evafc003/Mecatronica-Proyectos/Diagramas_y_Bocetos/Boceto_cascarrabias/RackandPinionGears(original)/images/RP_Cont_UpDown_Sz2.png

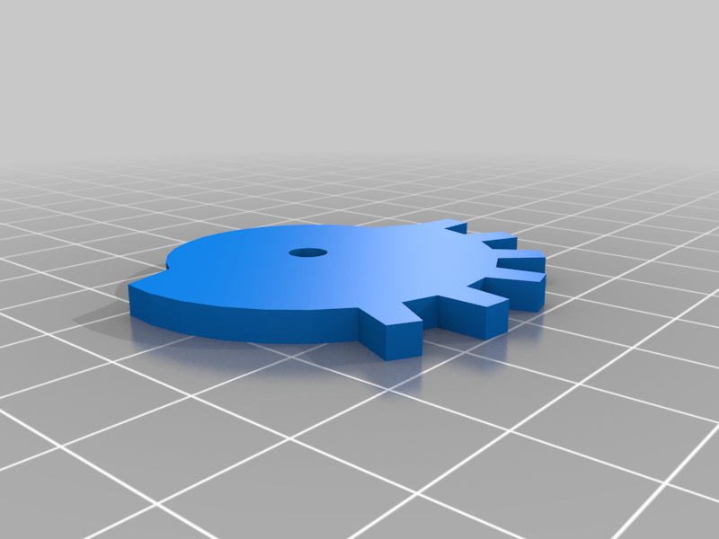
Diagramas_y_Bocetos/Boceto_cascarrabias/RackandPinionGears(original)/images/RP_Cont_UpDown_Sz2.png
