evafc003/Mecatronica-Proyectos/Diagramas_y_Bocetos/Diagrama_conexiones.png

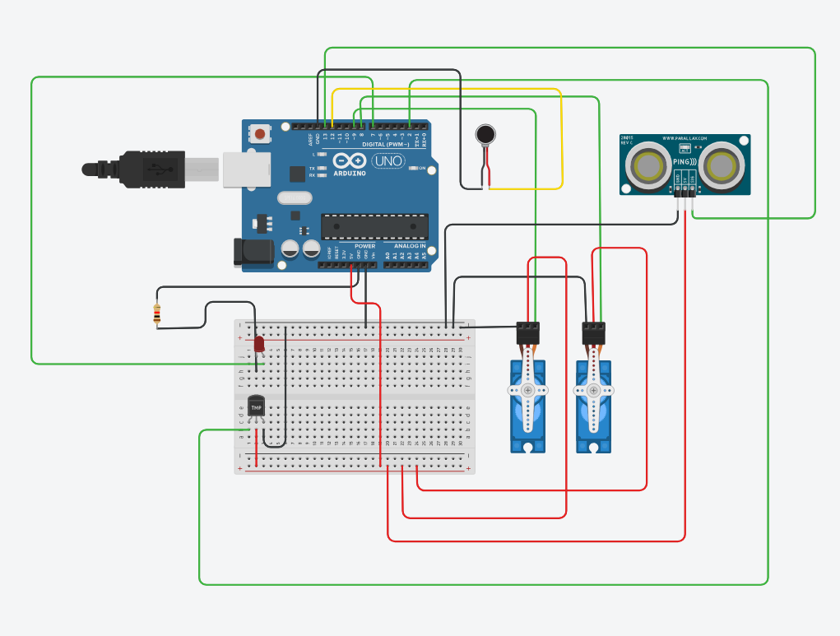
Diagramas_y_Bocetos/Diagrama_conexiones.png
