evafc003/Mecatronica-Proyectos/Multimedia/Fotos/caja_modificada.jpeg

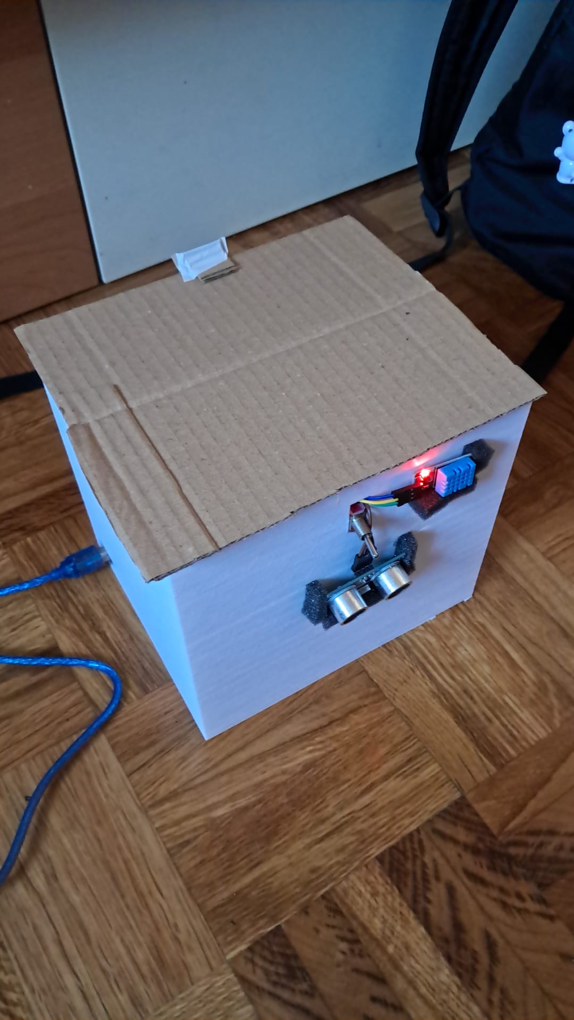
Multimedia/Fotos/caja_modificada.jpeg
