evafc003/Mecatronica-Proyectos/Multimedia/Fotos/cascarrabias_impreso.jpeg

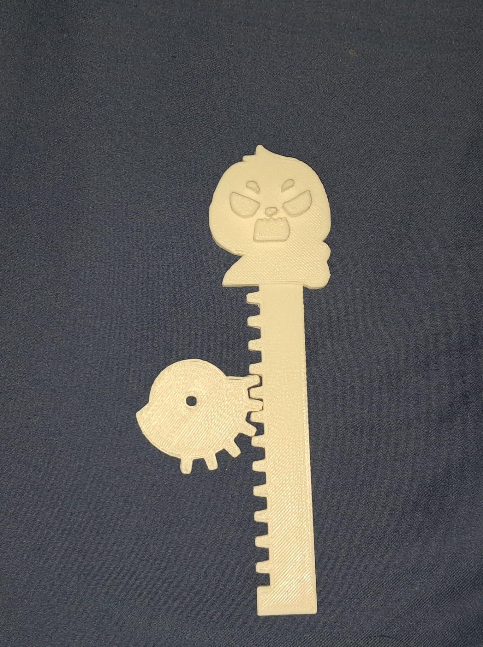
Multimedia/Fotos/cascarrabias_impreso.jpeg
