evafc003/Mecatronica-Proyectos/Multimedia/Fotos/montje_2_2.jpeg

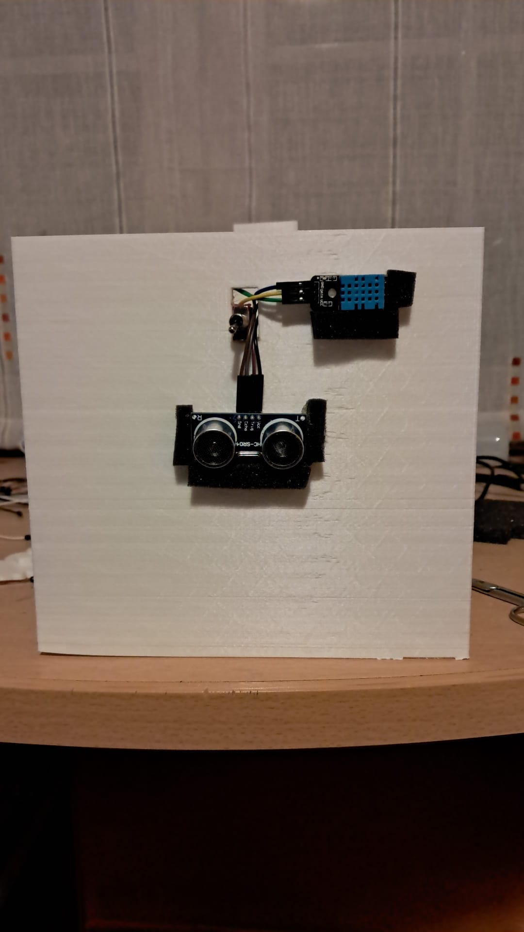
Multimedia/Fotos/montje_2_2.jpeg
