evafc003/Mecatronica-Proyectos/Multimedia/Fotos/Servo.png

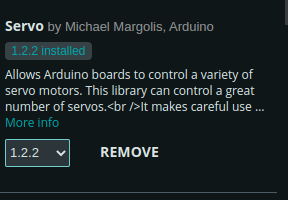
Multimedia/Fotos/Servo.png
