evafc003/Mecatronica-Proyectos/Multimedia/Fotos/tuto1.png

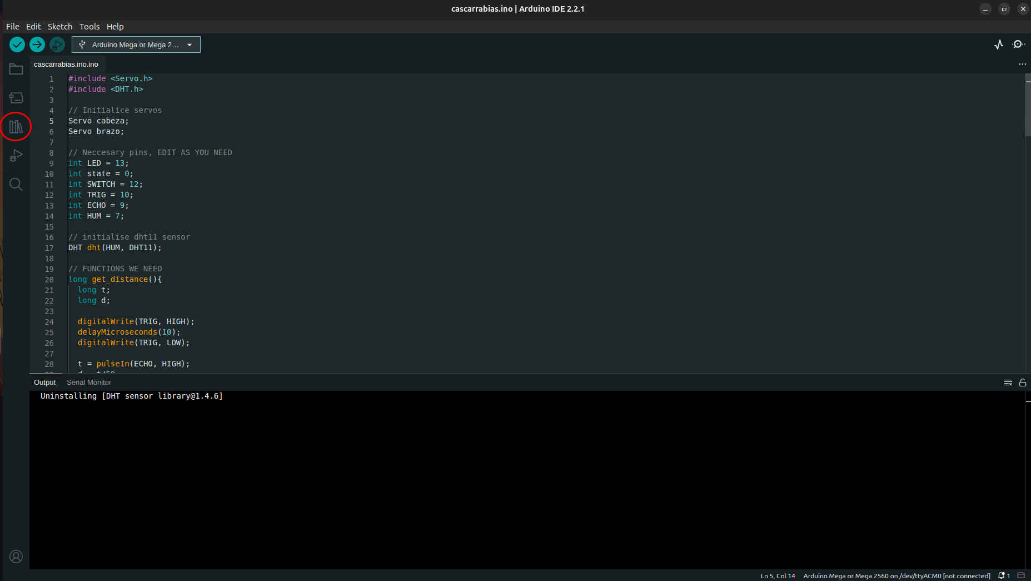
Multimedia/Fotos/tuto1.png
