evafc003/Mecatronica-Proyectos/Multimedia/Fotos/tuto2.png

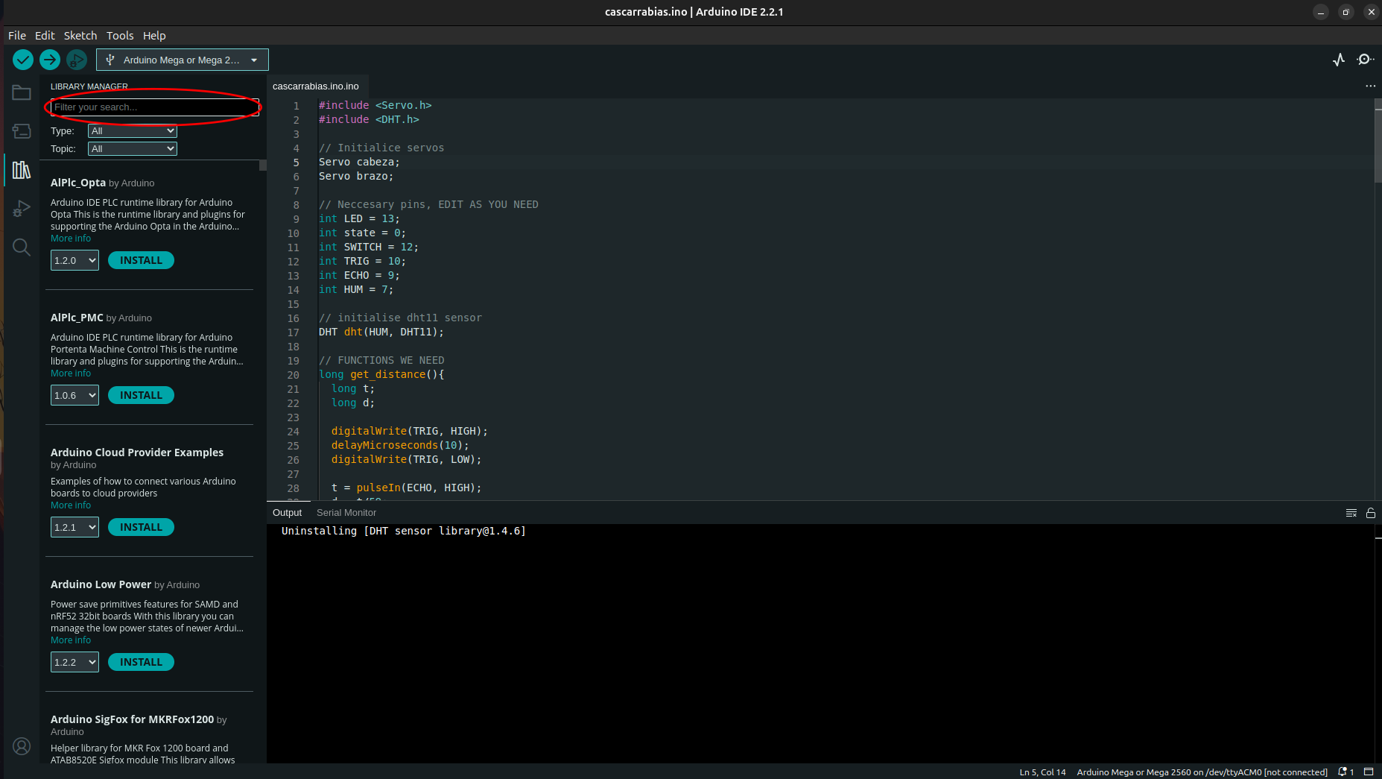
Multimedia/Fotos/tuto2.png
