evafc003/Mecatronica-Proyectos/Multimedia/Fotos/tuto5.png

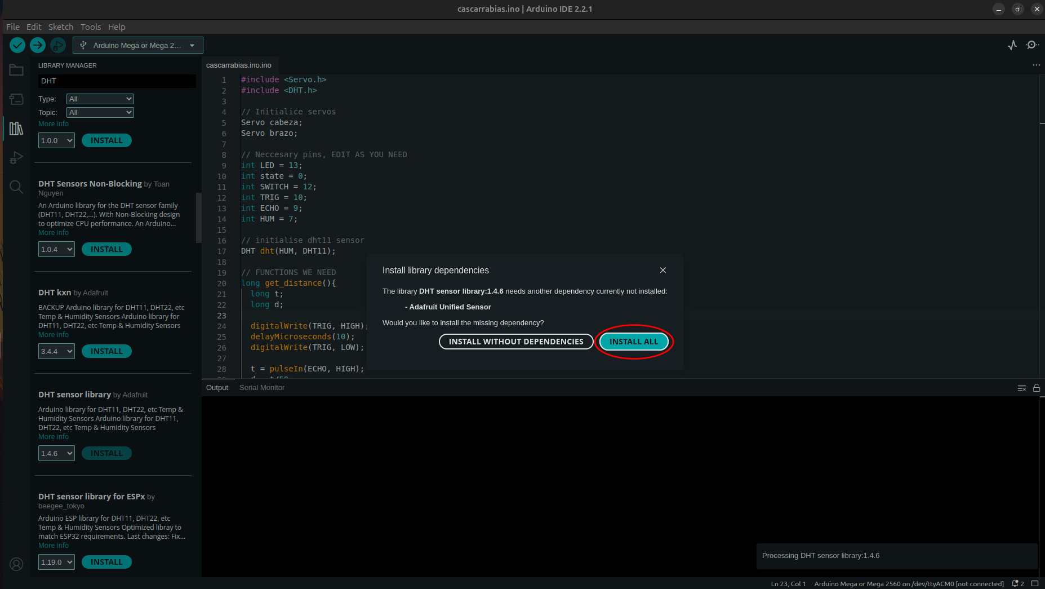
Multimedia/Fotos/tuto5.png
