evafc003/Mecatronica-Proyectos/Multimedia/Vídeos/mecanismo_brazo.gif

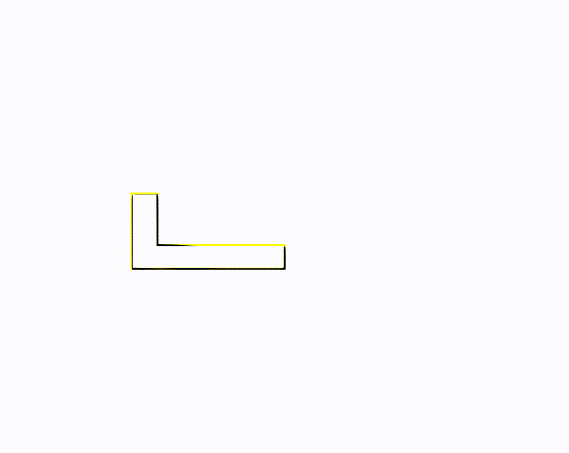
Multimedia/Vídeos/mecanismo_brazo.gif
