evafc003/Mecatronica-Proyectos/Planos/Planos_caja.jpeg

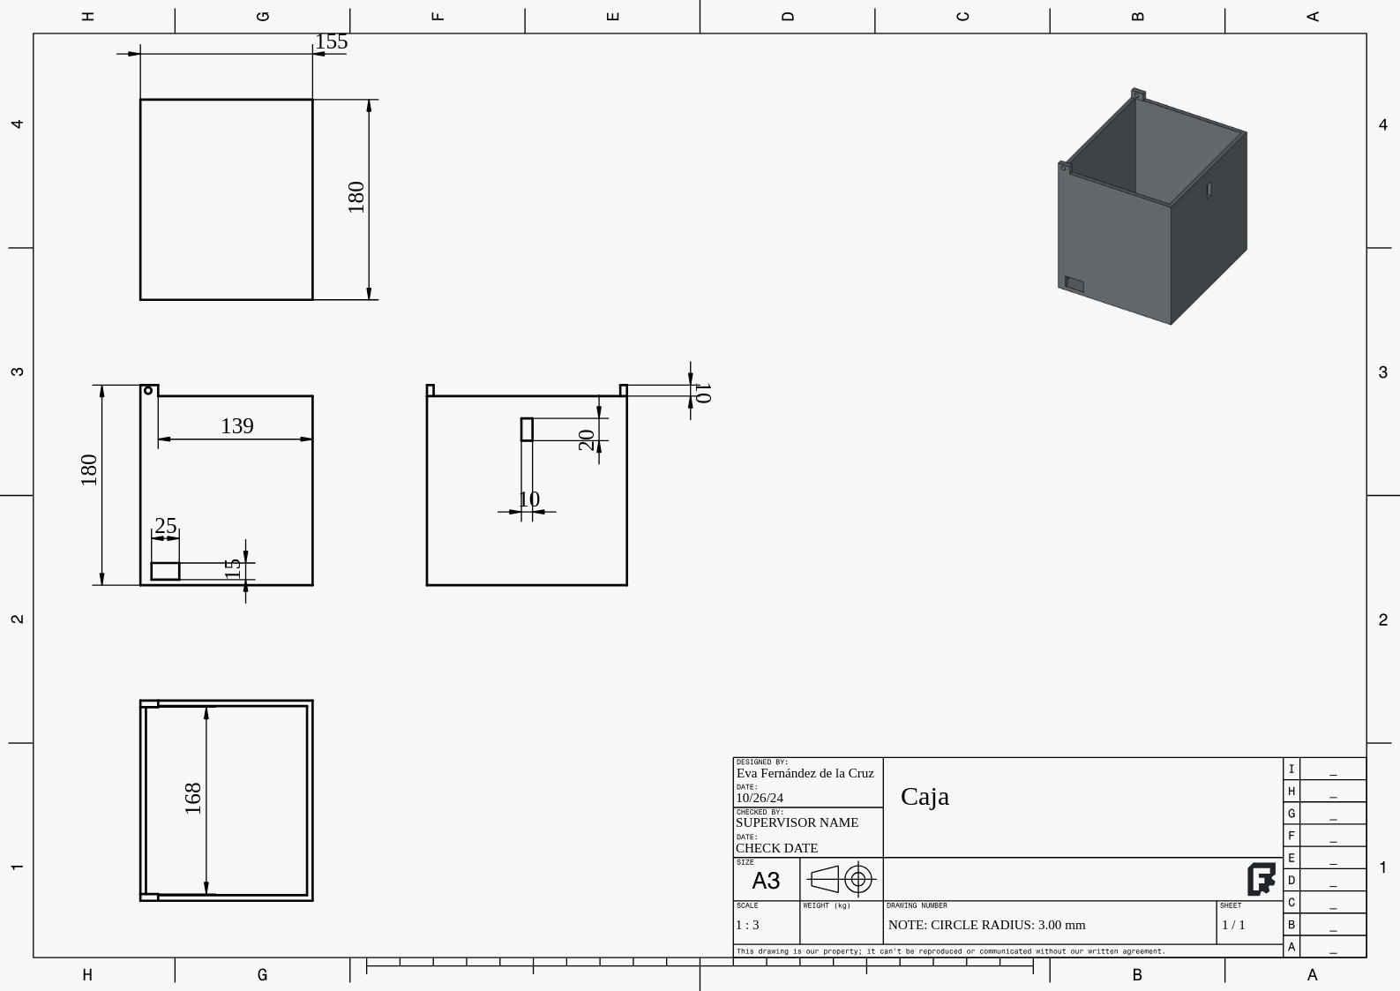
Planos/Planos_caja.jpeg
