evafc003/Mecatronica-Proyectos/Planos/Planos_tapa.jpeg

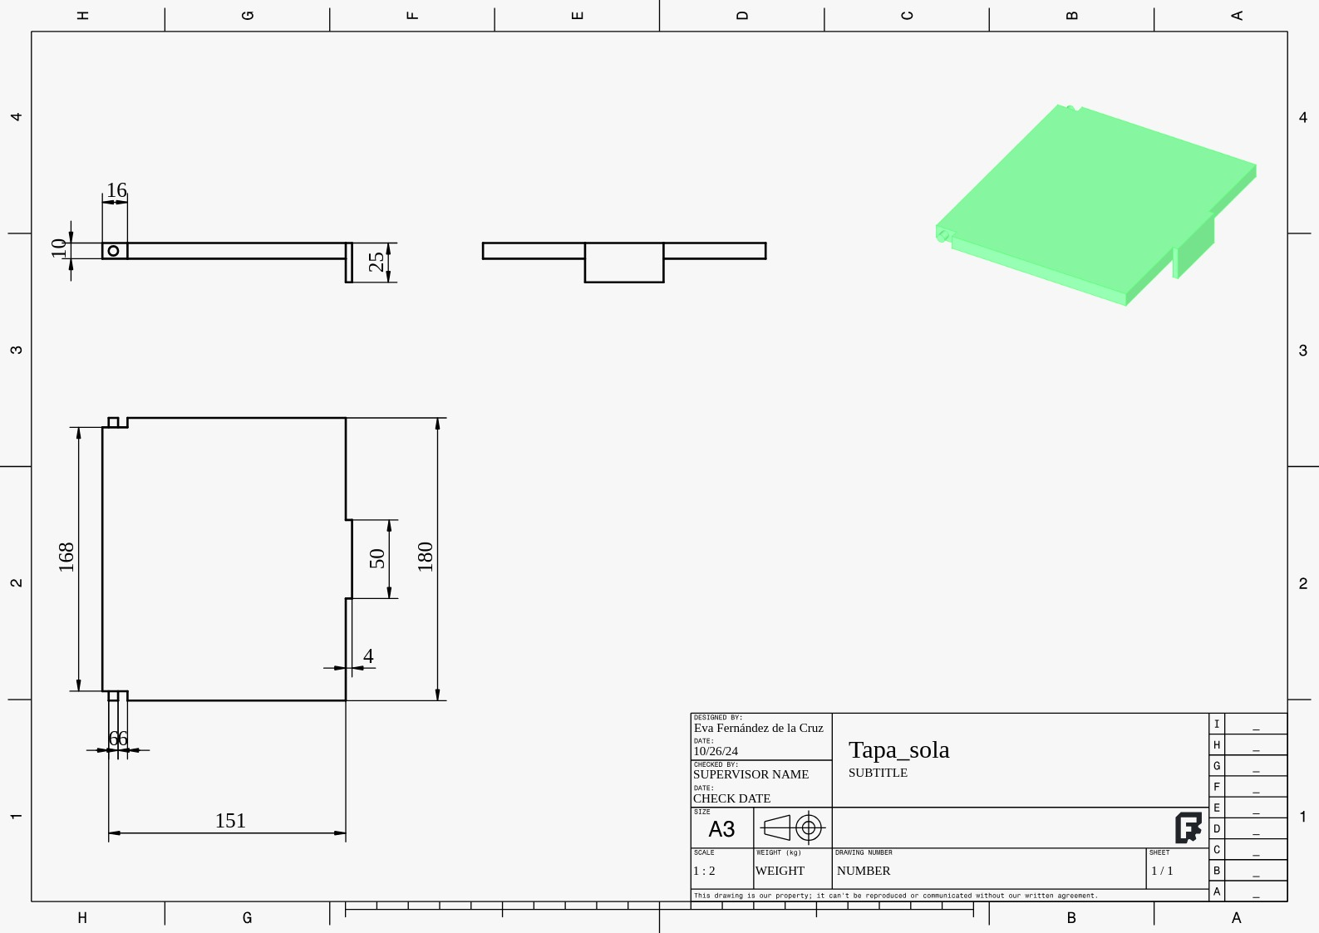
Planos/Planos_tapa.jpeg
