evafc003/Mecatronica-Proyectos/Diagramas_y_Bocetos/Boceto_cascarrabias/RackandPinionGears(original)/files/RP_Cont_UpDown_Sz2.stl

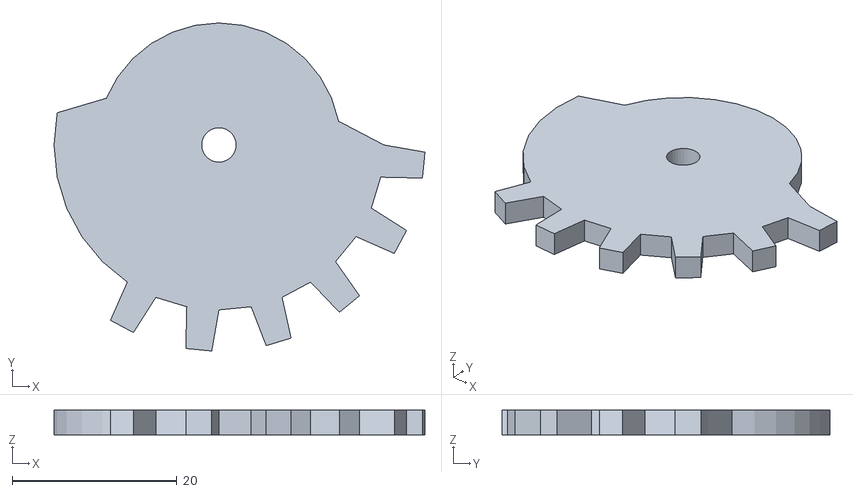
[picture p31: CAD file, 2024-11-06]
Diagramas_y_Bocetos/Boceto_cascarrabias/RackandPinionGears(original)/files/RP_Cont_UpDown_Sz2.stl
45.0 x 39.8 x 3.00
