evafc003/Mecatronica-Proyectos/Diagramas_y_Bocetos/plano_montaje_interior.jpeg

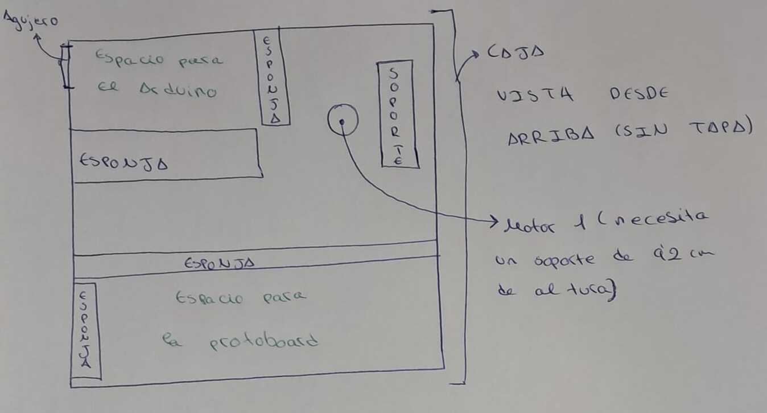
Diagramas_y_Bocetos/plano_montaje_interior.jpeg
