evafc003/Mecatronica-Proyectos/Diagramas_y_Bocetos/plano_montaje_motores.jpeg

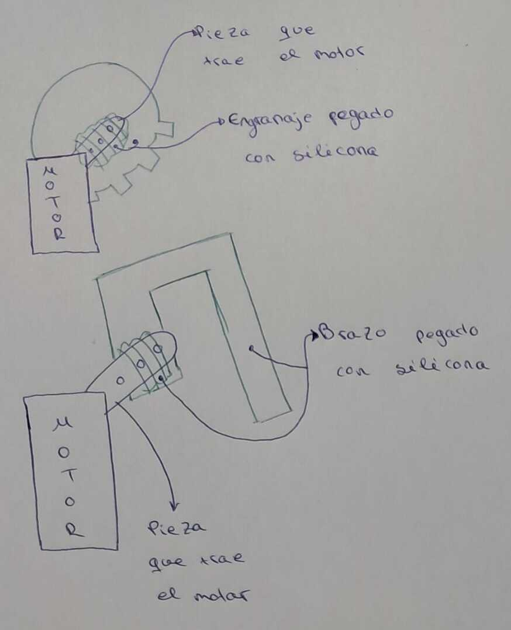
Diagramas_y_Bocetos/plano_montaje_motores.jpeg
