evafc003/Mecatronica-Proyectos/Multimedia/Fotos/montaje_2_1.jpeg

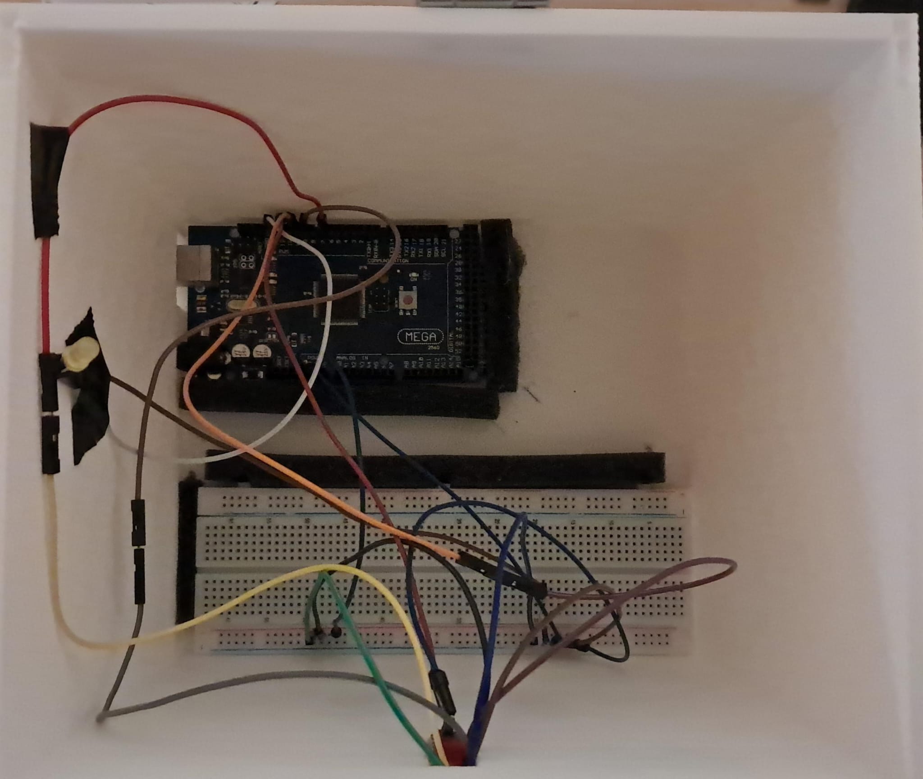
Multimedia/Fotos/montaje_2_1.jpeg
