evafc003/Mecatronica-Proyectos/Multimedia/Fotos/Montaje_V1.jpeg

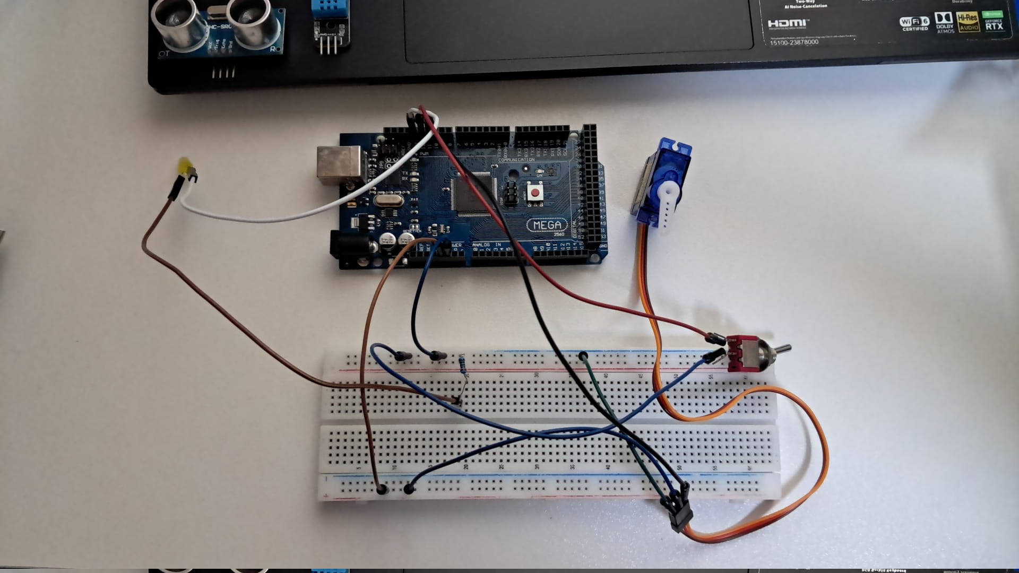
Multimedia/Fotos/Montaje_V1.jpeg
